chrisspen/ntp-clock-projector/docs/parts/Adafruit LED Backpack/878-00.jpg

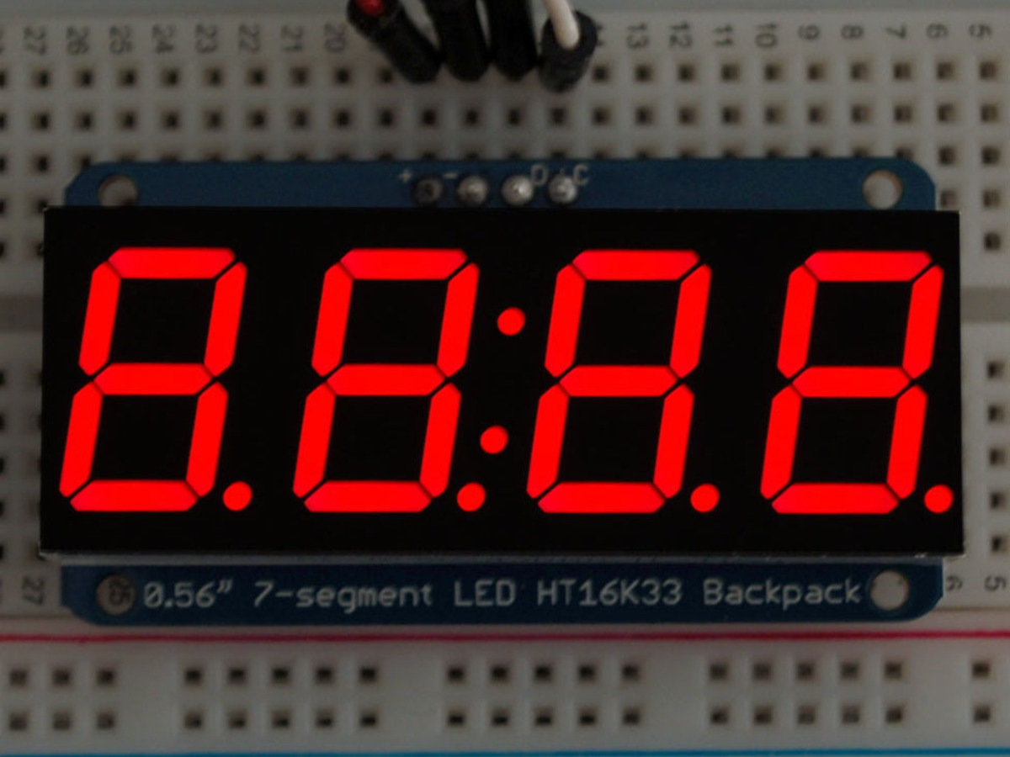
docs/parts/Adafruit LED Backpack/878-00.jpg
