chrisspen/ntp-clock-projector/models/housing_lid.scad

use <layout.scad>;

translate([0,0,0])
//rotate([0,180,0])
housing_lid(buffer=0, usb_cutout=1, mount_holes=1);
