chrisspen/ntp-clock-projector/models/lens_holder_bottom.scad

use <layout.scad>;

translate([0,0,0])
//rotate([0,180,0])
lens_holder_bottom();
