chrisspen/ntp-clock-projector/models/lens_worm_gear.scad

use <layout.scad>;

lens_holder_worm_gear(bb=0);
