chrisspen/ntp-clock-projector/models/rack.scad

use <layout.scad>;

translate([0,0,0])
rotate([90,0,0])
lens_holder_rack(bb=0, buffer=0);
