chrisspen/ntp-clock-projector/models/printable/base.png

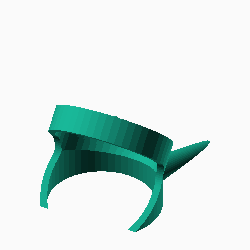
models/printable/base.png
