chrisspen/ntp-clock-projector/models/printable/housing.png

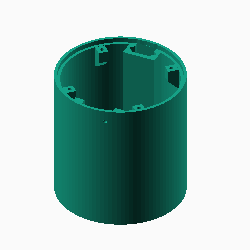
models/printable/housing.png
