chrisspen/ntp-clock-projector/models/printable/housing_lid.png

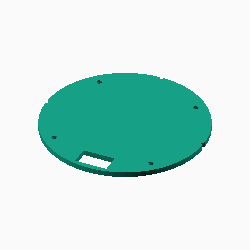
models/printable/housing_lid.png
