chrisspen/ntp-clock-projector/models/printable/rack.png

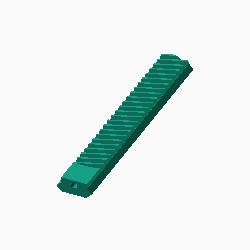
models/printable/rack.png
